fengyuan66/Highway-FlightSim/Assets/FCU_FULL.PNG

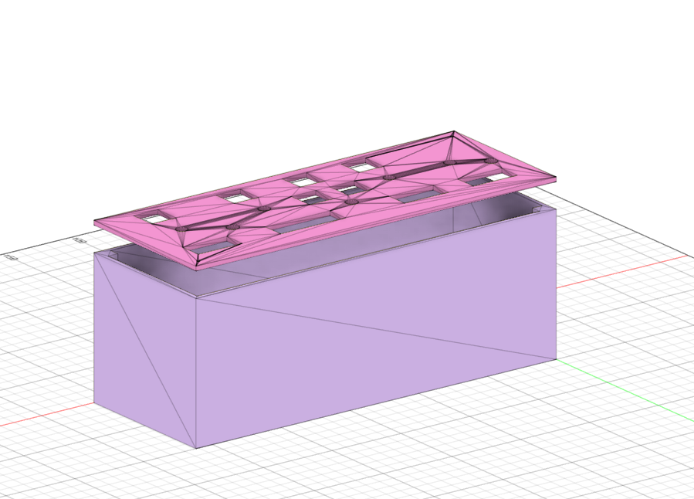
Assets/FCU_FULL.PNG
