fengyuan66/Highway-FlightSim/Assets/SecondTransfer/image.png

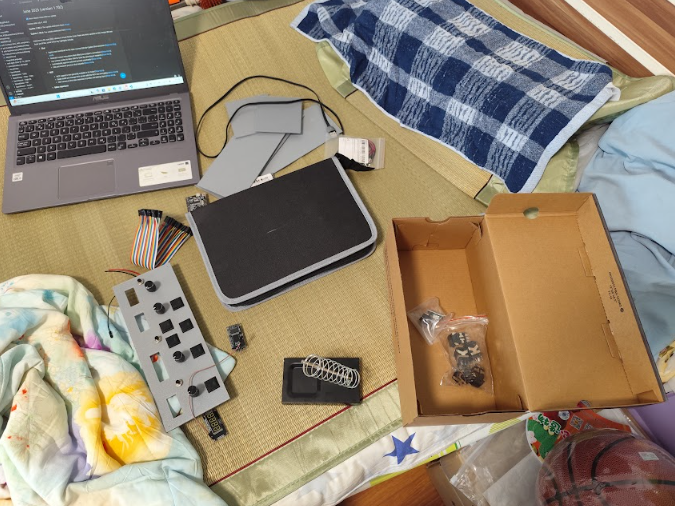
Assets/SecondTransfer/image.png
